SimGas/BME680-Datalogger-with-EINK-display/Code/preliminary tests/display/bme680_200_mono.h

#define bme680_200_mono_width 200
#define bme680_200_mono_height 58
static unsigned char bme680_200_mono_bits[] = {
   0x00, 0x00, 0x00, 0x00, 0x00, 0x00, 0x00, 0x00, 0x00, 0x00, 0x00, 0x00,
   0x00, 0x00, 0x00, 0x00, 0x00, 0x00, 0x00, 0x00, 0x00, 0x00, 0x00, 0x00,
   0x00, 0x00, 0x00, 0x00, 0x00, 0x00, 0x00, 0x00, 0x00, 0x00, 0x00, 0x00,
   0x00, 0x00, 0x00, 0x00, 0x00, 0x00, 0x00, 0x00, 0x00, 0x00, 0x00, 0x00,
   0x00, 0x00, 0x00, 0x00, 0x00, 0x00, 0x00, 0x00, 0x00, 0x00, 0x00, 0x00,
   0x00, 0x00, 0x00, 0x00, 0x00, 0x00, 0x00, 0x00, 0x00, 0x00, 0x00, 0x00,
   0x00, 0x00, 0x00, 0x00, 0x00, 0x00, 0x00, 0x00, 0x00, 0x00, 0x00, 0x00,
   0x00, 0x00, 0x00, 0x00, 0x00, 0x00, 0x00, 0x00, 0x00, 0x00, 0x00, 0x00,
   0x00, 0x00, 0x00, 0x00, 0x00, 0x00, 0x00, 0x00, 0x00, 0x00, 0x00, 0x00,
   0x00, 0x00, 0x00, 0x00, 0x00, 0x00, 0x00, 0x00, 0x00, 0x00, 0x00, 0x00,
   0x00, 0x00, 0x00, 0x00, 0x00, 0x00, 0x00, 0x00, 0x00, 0x00, 0x00, 0x00,
   0x00, 0x00, 0x00, 0x00, 0x00, 0x00, 0x00, 0x00, 0x00, 0x00, 0x00, 0x00,
   0x00, 0x00, 0x00, 0x00, 0x00, 0x00, 0x00, 0x00, 0x00, 0x00, 0x00, 0x00,
   0x00, 0x00, 0x00, 0x00, 0x00, 0x00, 0x00, 0x00, 0x00, 0x00, 0x00, 0x00,
   0x00, 0x00, 0x00, 0x00, 0x00, 0x00, 0x00, 0x00, 0x00, 0x00, 0x00, 0x00,
   0x00, 0x00, 0x00, 0x00, 0x00, 0x00, 0x00, 0x00, 0x00, 0x00, 0x00, 0x00,
   0x00, 0x00, 0x00, 0x00, 0x00, 0x00, 0x00, 0x00, 0x00, 0x00, 0x02, 0x00,
   0x00, 0x00, 0x00, 0x00, 0x00, 0x00, 0x00, 0x00, 0x00, 0x00, 0x00, 0x00,
   0x00, 0x00, 0x00, 0x00, 0x00, 0x00, 0x00, 0x00, 0x00, 0x00, 0x00, 0x03,
   0x00, 0x00, 0x00, 0x00, 0x00, 0x80, 0x03, 0x00, 0x00, 0x00, 0x00, 0x00,
   0x00, 0x00, 0x00, 0x00, 0x00, 0x00, 0x00, 0x00, 0x00, 0x00, 0x00, 0x00,
   0x03, 0x00, 0x00, 0x00, 0x00, 0x00, 0xe0, 0x0f, 0x00, 0x00, 0x00, 0x00,
   0x00, 0x00, 0x01, 0x00, 0x00, 0x00, 0x00, 0x00, 0x00, 0x00, 0x00, 0x00,
   0x00, 0x00, 0xc0, 0x01, 0x00, 0x00, 0x00, 0xe0, 0x1f, 0x00, 0x00, 0x00,
   0x00, 0x00, 0x80, 0x03, 0x00, 0x00, 0xe0, 0x00, 0x00, 0x00, 0x00, 0x00,
   0x80, 0x01, 0x00, 0xc6, 0x01, 0x00, 0x00, 0x00, 0xf0, 0x1e, 0x00, 0x00,
   0x00, 0x00, 0x00, 0xc0, 0x03, 0x00, 0x00, 0xf8, 0x07, 0x00, 0x00, 0x00,
   0x00, 0x00, 0x83, 0x0f, 0xf3, 0x01, 0x00, 0x00, 0x00, 0x70, 0x1c, 0x00,
   0x00, 0x00, 0x00, 0xc0, 0x40, 0x04, 0x00, 0x00, 0x0c, 0x0c, 0x00, 0x80,
   0x01, 0x00, 0x00, 0xe2, 0x3f, 0xb0, 0x00, 0x00, 0x00, 0x04, 0x70, 0x1c,
   0x00, 0x00, 0x00, 0x00, 0xe0, 0x61, 0x0c, 0x00, 0x00, 0x06, 0x08, 0x00,
   0xe0, 0x07, 0x00, 0x00, 0x38, 0x70, 0xd8, 0x00, 0x00, 0x00, 0x04, 0x70,
   0x1c, 0x00, 0x00, 0x00, 0x00, 0xf0, 0x33, 0x08, 0x00, 0x00, 0x02, 0x18,
   0x00, 0x30, 0x0c, 0x00, 0x00, 0x1c, 0xc0, 0x4c, 0x00, 0x00, 0x00, 0x04,
   0x70, 0x1c, 0x00, 0x00, 0x00, 0x00, 0xf0, 0x13, 0x18, 0x00, 0x00, 0x02,
   0x10, 0x00, 0x10, 0x18, 0x00, 0x00, 0x0c, 0x80, 0x66, 0x00, 0x00, 0x80,
   0x3f, 0x70, 0x1e, 0x00, 0x00, 0x00, 0x00, 0xf8, 0x1f, 0x30, 0x00, 0x00,
   0x02, 0x10, 0x00, 0x18, 0x10, 0x00, 0x00, 0x06, 0x80, 0x33, 0x00, 0x00,
   0x80, 0x3f, 0x70, 0x1e, 0x00, 0x00, 0x00, 0x00, 0x3c, 0x0f, 0x20, 0x00,
   0x00, 0x02, 0x10, 0x00, 0x38, 0x10, 0x00, 0x00, 0x06, 0x80, 0x33, 0x00,
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
