SimGas/BME680-Datalogger-with-EINK-display/Code/preliminary tests/v1/v1/p_40.h

#define p_40_width 40
#define p_40_height 40
static unsigned char p_40_bits[] = {
   0x00, 0x10, 0x00, 0x00, 0x00, 0x00, 0x10, 0x00, 0x00, 0x00, 0x00, 0x10,
   0x00, 0x07, 0x00, 0x10, 0x00, 0x10, 0x07, 0x00, 0x20, 0xfe, 0xc1, 0x02,
   0x00, 0x80, 0x83, 0x63, 0x03, 0x00, 0xc0, 0x01, 0x36, 0x01, 0x00, 0xc0,
   0x00, 0x94, 0x01, 0x00, 0x60, 0x00, 0xcc, 0x00, 0x00, 0x60, 0x00, 0xcc,
   0x00, 0x00, 0x20, 0x00, 0x6c, 0x00, 0x00, 0x2e, 0x7e, 0xe6, 0x07, 0x00,
   0xe0, 0xff, 0xf1, 0x1f, 0x00, 0xf0, 0xe7, 0x31, 0x3e, 0x00, 0xf0, 0xc0,
   0x10, 0x38, 0x00, 0x78, 0x60, 0x08, 0x70, 0x00, 0x38, 0x30, 0x08, 0xf0,
   0x00, 0x18, 0x30, 0x0c, 0xf0, 0x01, 0x1c, 0x18, 0x0c, 0xf0, 0x07, 0x0c,
   0x08, 0x06, 0xf0, 0x0f, 0x0c, 0x06, 0x03, 0x00, 0x0e, 0x0c, 0x07, 0x03,
   0x00, 0x0e, 0x8c, 0x83, 0x01, 0xf0, 0x1f, 0x8c, 0x81, 0x01, 0xfc, 0x1f,
   0xdc, 0xc0, 0x00, 0x0e, 0x1c, 0x7c, 0xc0, 0x00, 0x07, 0x10, 0x78, 0x60,
   0x80, 0x01, 0x30, 0x38, 0x60, 0xc0, 0x01, 0x60, 0x08, 0x30, 0x40, 0x00,
   0x40, 0x0c, 0xf0, 0x7f, 0x70, 0xc0, 0x0c, 0xf0, 0x7f, 0x90, 0xc0, 0x06,
   0xf8, 0x7f, 0x70, 0xc0, 0x02, 0xf8, 0x7f, 0x10, 0xc0, 0x33, 0x0c, 0x60,
   0x10, 0xc0, 0x33, 0x04, 0x40, 0x00, 0xc0, 0x33, 0x06, 0xc0, 0x00, 0x40,
   0x06, 0x03, 0x80, 0x01, 0x30, 0xcc, 0x01, 0x00, 0x03, 0x10, 0xf8, 0x00,
   0x00, 0x0e, 0x0e, 0x00, 0x00, 0x00, 0xf8, 0x03 };
