SimGas/BME680-Datalogger-with-EINK-display/Code/preliminary tests/v1/v1/rh_40.h

#define rh_40_width 40
#define rh_40_height 40
static unsigned char rh_40_bits[] = {
   0x00, 0x00, 0x80, 0x00, 0x00, 0x00, 0x00, 0xc0, 0x01, 0x00, 0x00, 0x00,
   0xe0, 0x01, 0x00, 0x00, 0xc0, 0x20, 0x02, 0x00, 0x00, 0xf0, 0x13, 0x04,
   0x00, 0x00, 0xf0, 0x13, 0x0c, 0x00, 0x00, 0xf0, 0x0f, 0x08, 0x00, 0x00,
   0x38, 0x0f, 0x08, 0x00, 0x00, 0x18, 0x06, 0x10, 0x00, 0x00, 0x1c, 0x06,
   0x10, 0x00, 0x00, 0x0e, 0x02, 0x30, 0x00, 0x00, 0x0e, 0x0b, 0x20, 0x00,
   0x80, 0x07, 0x0b, 0x20, 0x00, 0x80, 0x03, 0x12, 0x24, 0x00, 0xc0, 0x03,
   0x76, 0x33, 0x00, 0xe0, 0x01, 0xc6, 0x11, 0x00, 0xe0, 0x01, 0x0c, 0x10,
   0x00, 0xf0, 0x00, 0x08, 0x08, 0x00, 0x70, 0x00, 0xf0, 0x0f, 0x00, 0x70,
   0x00, 0xe0, 0x07, 0x00, 0x38, 0x00, 0x00, 0x0f, 0x00, 0x18, 0x00, 0x00,
   0x0e, 0x00, 0x18, 0x03, 0x00, 0x7e, 0x00, 0x18, 0x03, 0x00, 0xcf, 0x03,
   0x1c, 0x03, 0x80, 0x03, 0x06, 0x1c, 0x03, 0xc0, 0x00, 0x0c, 0x18, 0x03,
   0x40, 0x00, 0x08, 0x18, 0x03, 0x60, 0x00, 0x10, 0x18, 0x06, 0x30, 0x4e,
   0x12, 0x38, 0x0c, 0x30, 0x52, 0x12, 0x30, 0x18, 0x36, 0xce, 0x13, 0x70,
   0xf0, 0x37, 0x4a, 0x12, 0xf0, 0xc0, 0x30, 0x52, 0x12, 0xe0, 0x01, 0x30,
   0x00, 0x10, 0xc0, 0x07, 0x70, 0x00, 0x08, 0x80, 0x1f, 0xfe, 0x00, 0x08,
   0x00, 0xfc, 0x0f, 0x03, 0x06, 0x00, 0xf0, 0x03, 0xee, 0x03, 0x00, 0x00,
   0x00, 0x78, 0x00, 0x00, 0x00, 0x00, 0x00, 0x00 };
