SimGas/BME680-Datalogger-with-EINK-display/Code/preliminary tests/v1/v1/sd_10.h

#define sd_10_width 9
#define sd_10_height 10
static unsigned char sd_10_bits[] = {
   0xfc, 0x01, 0x56, 0x01, 0x55, 0x01, 0xfd, 0x01, 0x93, 0x01, 0x5d, 0x01,
   0x5b, 0x01, 0x57, 0x01, 0x99, 0x01, 0xff, 0x01 };
