SimGas/BME680-Datalogger-with-EINK-display/Code/preliminary tests/v1/v1/t_40.h

#define t_40_width 40
#define t_40_height 40
static unsigned char t_40_bits[] = {
   0x00, 0x00, 0x0e, 0x00, 0x00, 0x00, 0x80, 0x1f, 0x00, 0x00, 0x00, 0x80,
   0x3f, 0x00, 0x00, 0x00, 0xc0, 0x3b, 0x00, 0x00, 0x20, 0xc0, 0x31, 0x00,
   0x00, 0x20, 0xc0, 0x31, 0x00, 0x00, 0x20, 0xc0, 0x31, 0x00, 0x00, 0xf8,
   0xc1, 0x39, 0x00, 0x00, 0xf8, 0xc1, 0x39, 0x00, 0x00, 0x20, 0xc0, 0x31,
   0x00, 0x00, 0x20, 0xc0, 0x31, 0x00, 0x00, 0x20, 0xc0, 0x31, 0x00, 0x00,
   0x00, 0xc0, 0x31, 0x00, 0x00, 0x00, 0xc0, 0x33, 0x00, 0x00, 0xfe, 0xff,
   0xff, 0xff, 0x0f, 0x00, 0xc0, 0x3f, 0x00, 0x00, 0x00, 0xc0, 0x31, 0x00,
   0x00, 0x00, 0xc0, 0x31, 0x00, 0x00, 0x00, 0xc0, 0x31, 0x00, 0x00, 0x00,
   0xc0, 0x39, 0x00, 0x00, 0x00, 0xc0, 0x31, 0x00, 0x00, 0x00, 0xc0, 0x31,
   0x00, 0x00, 0x00, 0xc0, 0x31, 0xe0, 0x00, 0x00, 0xc0, 0x31, 0xf8, 0x07,
   0x00, 0xc0, 0x31, 0x0e, 0x0e, 0x00, 0xc0, 0x31, 0x03, 0x08, 0x00, 0xe0,
   0xf1, 0x01, 0x10, 0x00, 0xf0, 0xf1, 0x00, 0x30, 0x00, 0x70, 0x64, 0x00,
   0x20, 0x00, 0x30, 0x6e, 0xe0, 0x60, 0x00, 0x30, 0x6e, 0x40, 0x60, 0x00,
   0x30, 0x6e, 0x40, 0x60, 0x00, 0x70, 0x60, 0x40, 0x60, 0x00, 0xf0, 0x60,
   0x40, 0x60, 0x00, 0xf0, 0x71, 0x00, 0x20, 0x00, 0xe0, 0xff, 0x00, 0x30,
   0x00, 0x00, 0x0f, 0x01, 0x10, 0x00, 0x00, 0x00, 0x06, 0x0c, 0x00, 0x00,
   0x00, 0x0c, 0x07, 0x00, 0x00, 0x00, 0xf0, 0x01 };
