SimGas/BME680-Datalogger-with-EINK-display/Code/preliminary tests/v1/v1/voc_40.h

#define voc_40_width 40
#define voc_40_height 40
static unsigned char voc_40_bits[] = {
   0x70, 0x00, 0x00, 0x00, 0x00, 0xfc, 0x01, 0x00, 0x00, 0x00, 0x06, 0x03,
   0x00, 0x30, 0x00, 0x03, 0x02, 0x00, 0xfc, 0x00, 0x01, 0x06, 0x00, 0x86,
   0x01, 0x01, 0x04, 0x00, 0x02, 0x01, 0x01, 0x04, 0x00, 0x03, 0x02, 0x03,
   0x0e, 0x00, 0x0f, 0x01, 0x02, 0x0e, 0x80, 0x19, 0x01, 0x86, 0x11, 0xc0,
   0x90, 0x01, 0xfc, 0xf0, 0x67, 0xf8, 0x00, 0xc0, 0xe0, 0x3f, 0x0c, 0x00,
   0x80, 0xc0, 0x3f, 0x06, 0x00, 0x00, 0x81, 0x7d, 0x03, 0x00, 0x00, 0x83,
   0xf0, 0x01, 0x00, 0x00, 0xc6, 0xe0, 0x01, 0x00, 0x00, 0x7f, 0xe0, 0x01,
   0x00, 0x00, 0x3f, 0xc0, 0x01, 0x00, 0x00, 0x07, 0xc0, 0x01, 0x00, 0x00,
   0x07, 0xc0, 0x01, 0x00, 0x00, 0x07, 0xf0, 0x01, 0x00, 0x00, 0x07, 0xf0,
   0x01, 0x00, 0x00, 0x0f, 0x08, 0xe3, 0x03, 0x00, 0x1f, 0x08, 0x7e, 0x0e,
   0x80, 0x7f, 0x08, 0x0e, 0x18, 0x80, 0xfc, 0x1f, 0x06, 0x30, 0x40, 0xf8,
   0x3f, 0x03, 0x60, 0x78, 0xcc, 0xef, 0x01, 0xc0, 0x7c, 0x04, 0xc0, 0x00,
   0x80, 0x62, 0x02, 0x80, 0xc6, 0xb8, 0x43, 0x03, 0x40, 0x61, 0x85, 0x83,
   0x01, 0x40, 0xed, 0x99, 0x03, 0x01, 0x40, 0x29, 0xa1, 0x82, 0x01, 0x80,
   0x26, 0x9d, 0x86, 0x00, 0x80, 0x01, 0xc0, 0x7c, 0x00, 0x00, 0x03, 0x60,
   0x00, 0x00, 0x00, 0x02, 0x20, 0x00, 0x00, 0x00, 0x0c, 0x18, 0x00, 0x00,
   0x00, 0x38, 0x0e, 0x00, 0x00, 0x00, 0xe0, 0x03 };
